mattdeeds/pico-10base-t-rs/docs/router-plan.md

# RP2350 wireless router — design plan

The end goal the whole project serves (see the `project-vision-router` memory):
a **low-power wireless router on the RP2350**. Wireless clients associate on the
LAN side; their traffic is **NAT-routed out the 10BASE-T WAN** to a wired
network / the internet.

With R0–R12e the **WAN half is essentially done** — a robust 10BASE-T NIC
(PIO Manchester TX/RX, edge-track DPLL, multicore RX, carrier-sense + CSMA/CA;
~742 kB/s idle, no starvation, 10–38× better under load than the old
single-core). This doc scopes the **router half**: the wireless LAN, the
forwarding/NAT data path, and how they fit our Hazard3 RISC-V / `rp235x-hal` /
no-embassy stack.

Status: **scoping (2026-05-28).** Architecture fork decided = **Option A**
(keep RISC-V, port the cyw43 transport — see §4). No router code written yet.

---

## 1. Target topology

```
   wireless clients (phones/laptops)
            │  (WPA2, 2.4 GHz)
            ▼
   ┌─────────────────────────────────────────────┐
   │  Pico 2 W (RP2350)                            │
   │                                               │
   │   LAN: CYW43439 in AP mode                    │
   │     • SSID + WPA2, DHCP server, gateway IP    │
   │            │                                  │
   │     ┌──────┴───────┐  forwarding + NAPT       │
   │     │  router core │  (conntrack TCP/UDP/ICMP)│
   │     └──────┬───────┘                          │
   │            │                                  │
   │   WAN: 10BASE-T NIC (R0–R12e)                 │
   │     • DHCP client, default route, DNS         │
   └────────────┼──────────────────────────────────┘
                ▼
        wired LAN / internet
```

The 10BASE-T WAN (~6 Mbit/s effective) is the throughput bottleneck — fine for
a "low-power router." The CYW43 2.4 GHz LAN has headroom to spare.

## 2. What we have vs. what a router needs

| Piece | Have? | Notes |
|---|---|---|
| WAN PHY (10BASE-T) | ✅ R0–R12e | PIO TX/RX, DPLL, multicore RX, CSMA/CA |
| Endpoint stack (the device's own IP) | ✅ smoltcp | ARP/ICMP/UDP/TCP terminate today |
| LAN PHY (wireless AP) | ❌ | CYW43439 in AP mode (§5) |
| DHCP **client** (WAN) | ❌ | smoltcp has a `dhcpv4` socket — small |
| DHCP **server** (LAN) | ❌ | smoltcp has no server — new code (§6.3) |
| L3 **forwarding** between interfaces | ❌ | new — smoltcp won't (§3, §6.1) |
| **NAPT** + connection tracking | ❌ | new — the bulk of the work (§6.2) |
| DNS relay (LAN → WAN) | ❌ | new-ish (§6.4) |
| Management UI | ◑ | reuse the HTTP server on the LAN gateway IP |

## 3. smoltcp's role — keep it, but it is NOT the router

smoltcp is an **endpoint** TCP/IP stack: an `Interface` owns sockets and
terminates traffic addressed to its own IP(s). It has **no packet forwarding
between interfaces and no NAT/NAPT** — it drops anything not addressed to it.

So the router splits cleanly into two planes:

- **Control plane → smoltcp (keep it).** The device's *own* traffic on *both*
  interfaces: DHCP client (WAN), DNS resolver, the management HTTP/UI, ICMP.
  And `cyw43` exposes a **`NetDriver` that plugs straight into a smoltcp
  `Interface`** — the standard, supported LAN glue. Ripping smoltcp out would
  be a mistake; it's doing real work.
- **Data plane → NEW custom code.** Transit packets (a LAN client → the
  internet, and the return path) bypass smoltcp entirely: parse the IP packet,
  NAPT-rewrite it, re-emit on the other interface.

**Architecture = hybrid with a per-frame classifier.** A frame arriving on
either interface is classified:
- **for-us** (dst MAC = our iface MAC, dst IP = our iface IP, broadcast/ARP,
  or a NAPT-return flow) → hand to that interface's smoltcp `Interface`, OR to
  the NAPT reverse path;
- **transit** (routable, not for us) → the forwarding + NAPT fast-path.

This matches the `project-vision-router` instinct ("per-interface raw frames +
our own forwarding/NAPT layer") — but only for the *fast path*; smoltcp stays
the control-plane brain. Two smoltcp `Interface`s (one per phy) coexist with the
forwarding layer; they don't talk to each other through smoltcp.

## 4. The architecture fork — DECIDED: Option A (keep RISC-V)

**The finding that drove this:** the CYW43 driver ecosystem (`cyw43`,
`cyw43-pio`, `embassy-net`) is embassy-centric, and **embassy supports RP2350
only on the ARM Cortex-M33 cores** — to target the **Hazard3 RISC-V** cores you
drop embassy and use `rp235x-hal`, which is precisely our entire codebase. So
the stock wireless stack and our stack sit on opposite sides of an ARM↔RISC-V
line.

Options considered:

| Option | Keeps R0–R12e? | Wireless effort | Decision |
|---|---|---|---|
| **A. Keep RISC-V, port the cyw43 transport** | ✅ all | custom `SpiBusCyw43` + async glue | **CHOSEN** |
| B. Switch the project to ARM + embassy | ❌ rewrite NIC | cyw43 "just works" | rejected — throws away the Hazard3 multicore/PIO/DPLL work |
| C. External wireless (ESP32-AT over SPI) | ✅ | different driver | fallback only — not the onboard radio the user wants |

**Why Option A is feasible** (verified during scoping):
1. `cyw43`'s core driver is **transport-agnostic** via the `SpiBusCyw43` trait;
   `cyw43-pio`'s `PioSpi` is just the embassy-rp reference impl. We write our
   own `SpiBusCyw43` on `rp235x-hal`'s **free PIO1**.
2. `embassy-executor` has a real **`arch-riscv32`** backend (used by ESP32-C3/
   C6, which are riscv32imc/imac) — *separate* from the ARM-only `embassy-rp`
   HAL. So async tasks can run on Hazard3 (`riscv32imac`).
3. A small **`embassy-time-driver`** shim backed by our existing `rp235x-hal`
   `Timer` satisfies cyw43's `Timer::after` delays.

So we pull in `cyw43` (core) + arch-agnostic embassy support crates
(`embassy-executor` arch-riscv32, `embassy-time`, `embassy-sync`,
`embassy-futures`) and skip `embassy-rp` and `cyw43-pio` entirely. The
**biggest new infrastructure + risk is adopting an async runtime** on our
currently-blocking main loop — de-risked first (§7, R13).

## 5. Wireless integration design (Option A)

```
   cyw43 core (transport-agnostic)
     │  SpiBusCyw43 trait
     ▼
   OUR PioSpiCyw43  ── rp235x-hal PIO1 (half-duplex SPI) + DMA + CS/PWR pins
     │
     ├─ Runner::run()  ── async task, driven by embassy-executor (arch-riscv32)
     │                     uses embassy-time (our Timer shim) for delays
     │
     └─ Control         ── async: init(), start_ap_wpa2(SSID, pass), gpio_set(LED)…
     └─ NetDriver       ── impls a Device → smoltcp Interface (LAN control plane)
```

Open items to nail in the R13 spike:
- **Half-duplex SPI PIO program.** The CYW43 uses a nonstandard half-duplex
  SPI (shared data line). Reference: the pico-sdk `cyw43_bus_pio_spi.c` PIO
  program and embassy's `cyw43-pio` — port the program to `rp235x-hal`'s PIO
  API on PIO1.
- **Firmware blobs.** CYW43439 firmware (`43439A0.bin`) + CLM blob, loaded at
  runtime; embed in flash (`include_bytes!`) and feed to `cyw43::new`.
- **Async runtime shape.** embassy-executor on core 0 (restructure `main`'s
  poll loop into async tasks: cyw43 Runner, smoltcp poll×2, router). The
  10BASE-T PIO/DMA/core-1 RX path is IRQ-driven and stays as-is; an async task
  drains its inbox via smoltcp. Decide whether the cyw43 Runner shares core 0
  or moves to core 1 (see §6 core budget).
- **embassy-time-driver** on `rp235x-hal` `Timer` (TIMER0): implement the
  `embassy_time_driver::Driver` trait (now(), schedule_wake()).

## 6. Router data path (the new feature work)

### 6.1 Forwarding
Classify each received frame (§3). Transit IP packets: decrement TTL, look up
the egress interface (LAN-side = the AP subnet; everything else = default route
out WAN), re-emit. Start with plain forwarding (no NAT) tested via static host
routes, then layer NAPT on top.

### 6.2 NAPT + connection tracking
- Outbound (LAN→WAN): rewrite src IP→WAN IP, src port→an allocated port;
  insert/refresh a conntrack entry keyed by (proto, orig-src, orig-sport,
  dst, dport).
- Inbound (WAN→LAN): match the conntrack entry, rewrite dst back to the LAN
  client, re-emit on LAN.
- Per-proto: TCP (track via ports + a coarse state/timeout), UDP (ports +
  idle timeout), ICMP echo (track via id). Fix up IP + L4 checksums on rewrite
  (incremental checksum update).
- Fixed-size conntrack table (heapless) with LRU/timeout eviction — bounded RAM,
  no alloc. This is the bulk of the new code.

### 6.3 DHCP server (LAN)
smoltcp has only a DHCP *client*. The LAN DHCP server is new: a small UDP
responder (DISCOVER→OFFER, REQUEST→ACK) handing out leases from the AP subnet
pool, with gateway = our LAN IP and DNS = our LAN IP (we relay). Fixed lease
table.

### 6.4 DNS relay + management
- DNS: LAN clients use us as resolver; forward their queries out the WAN to the
  upstream DNS (learned via WAN DHCP), relay answers back. (Or run NAPT over the
  DNS UDP flow like any other — simplest is to just NAT port 53 through.)
- Management: reuse the existing HTTP server, bound to the LAN gateway IP —
  status (clients, conntrack, WAN link), and later config.

### Core / PIO / DMA / pin budget
- **PIO:** PIO0 = SM0 10BT-TX, SM1 10BT-RX, SM2 carrier-detect (SM3 free).
  **PIO1 → cyw43 half-duplex SPI** (1 SM). Fits.
- **DMA:** ch0/ch1 = 10BT RX double-buffer; cyw43 SPI wants 1–2 channels —
  available.
- **Cores:** core 0 = main/async-exec/WAN-TX/smoltcp×2/router/USB; core 1 =
  10BT RX decode. The cyw43 Runner + forwarding add load to core 0 — **open
  question:** may need to rebalance (e.g. forwarding fast-path or the cyw43
  Runner on core 1). Measure before deciding.
- **Pins (Pico 2 W):** the CYW43 consumes **GP23 (WL_ON), GP24 (WL_DATA),
  GP25 (WL_CS), GP29 (WL_CLK)**, and the user **LED moves onto the CYW43's own
  GPIO0**. Our 10BASE-T (GP13 RO, GP14 DI) is clear of all of these →
  coexists. **But GP25 (today's `led` pin) becomes WL_CS** — the LED code must
  move to the CYW43 GPIO (via the driver) or another free pin. *(Verify exact
  Pico 2 W pinout in R13.)*
- **Power:** "low-power" fights the always-on 60 MHz RX sampler + continuous
  DMA + cyw43. Deferred to last (roadmap E) — a known unresolved tension.

## 7. Phased roadmap

Riskiest piece (wireless on Hazard3) first, so Option A is proven before we
build the router on top of it.

| Phase | Goal | Acceptance |
|---|---|---|
| **R13 — wireless de-risk spike** | Custom `SpiBusCyw43` on PIO1 + embassy-executor(riscv32) + time-driver shim + CYW43 firmware load. | Chip inits; beacons (AP) or associates (STA); a client sees the SSID / the chip's own LED toggles via the driver. *Proves Option A.* |
| **R14 — LAN up** | CYW43 **AP mode** (WPA2) + smoltcp on its `NetDriver` + **DHCP server**. | A phone joins the SSID, gets a DHCP lease, pings the Pico's LAN gateway IP. |
| **R15 — WAN as client** | **DHCP client** on the 10BASE-T (smoltcp `dhcpv4`) → upstream IP, default route, DNS. | The Pico itself reaches the internet (ping 8.8.8.8, resolve a name). |
| **R16 — forwarding** | L3 forward LAN↔WAN for transit packets (static routes, no NAT). | A LAN client with a manual route reaches a WAN host. |
| **R17 — NAPT** | NAT/NAPT + conntrack (TCP/UDP/ICMP) + the per-frame classifier. | **A phone on WiFi browses the internet through the Pico.** The milestone. |
| **R18 — DNS relay + mgmt UI** | LAN DNS relay; HTTP status/config on the LAN gateway IP. | Clients resolve names via the Pico; mgmt page shows clients + WAN link. |
| **R19+ — robustness, backpressure, then low-power** | Flow control, conntrack pressure handling; then the deferred power work. | — |

## 8. Risks + open questions

1. **Async runtime adoption (R13, the #1 risk).** embassy-executor on
   `riscv32imac` is real but unproven *in this project*; restructuring the
   blocking main loop into async tasks touches everything. De-risk in R13 with
   the minimum (just blink the CYW43 LED via async) before committing.
2. **Half-duplex SPI PIO port.** The CYW43 SPI program must be ported to
   `rp235x-hal` PIO1. The pico-sdk C program + cyw43-pio are the references.
3. **Core balance.** cyw43 Runner + NAPT forwarding + two smoltcp polls on
   core 0 may not fit; rebalancing onto core 1 (which currently only decodes
   10BT RX) is the likely lever — measure, don't assume (the project's MO).
4. **Memory.** Two smoltcp `Interface`s + socket buffers + conntrack + DHCP/
   ARP tables + cyw43 firmware + core-1 stack. RP2350 has 520 KB SRAM — should
   fit, but budget it.
5. **Low-power vs always-on sampler** — unresolved; explicitly last.
6. **cyw43 on Hazard3 has little/no precedent** — we may hit
   embassy-executor/embassy-time integration rough edges that the ARM path
   doesn't. Keep Option C (external module) as the fallback if R13 stalls.

## 9. References

- cyw43 driver + AP mode + RP2350/Pico 2 W support: <https://docs.embassy.dev/cyw43>,
  <https://github.com/embassy-rs/embassy/tree/main/cyw43>
- embassy RISC-V on RP2350 = drop embassy, use rp235x-hal (ARM-only embassy):
  <https://riscv.org/blog/raspberry-pi-launch-new-rp2350-microcontroller-and-pico-2-development-board-with-risc-v-support/>
- embassy-executor `arch-riscv32`:
  <https://github.com/embassy-rs/embassy/blob/main/embassy-executor/src/arch/riscv32.rs>
- `SpiBusCyw43` / custom transport + the half-duplex SPI PIO:
  <https://github.com/embassy-rs/embassy/blob/main/cyw43-pio/src/lib.rs>,
  <https://github.com/raspberrypi/pico-sdk/blob/master/src/rp2_common/pico_cyw43_driver/cyw43_bus_pio_spi.c>

## 10. R13 progress — board-independent scaffolding DONE (2026-05-28)

Built on branch `r13-wireless-scaffold` (not merged). Gated behind a new
`wireless` cargo feature, OFF by default — the production 10BASE-T build is
byte-unchanged. **`cargo build --release --features wireless` compiles AND
links for `riscv32imac`.**

**De-risking results (the reason for the spike):**
- **cyw43 0.7.0 + its ARM-named deps (`cortex-m` 0.7.7, `cortex-m-rt` 0.7.5)
  compile for riscv32imac.** The fear that `cortex-m-rt` would `compile_error!`
  on non-ARM was wrong — it target-gates to ~nothing. So Option A is viable.
- **`embassy-executor` 0.10 `platform-riscv32` backend links on Hazard3** —
  the #1 risk (async runtime on RISC-V, separate from the ARM-only
  `embassy-rp`) is cleared at the link level.
- Compatible version set pinned by cyw43 0.7.0: embassy-time 0.5.1 (with
  `tick-hz-1_000_000` + `generic-queue-16`), embassy-time-driver 0.2.2,
  embassy-time-queue-utils 0.3.2, embassy-sync 0.8.0, embassy-futures 0.1.2.
  The executor feature is `platform-riscv32` (renamed from `arch-riscv32`).
- embassy-executor 0.10's `#[task]` macro returns a `Result<SpawnToken,_>`
  (arena slot) — spawn via `if let Ok(t) = task() { spawner.spawn(t) }`.

**What's in `src/wireless.rs` (compiles + links, not yet run on hardware):**
1. **embassy-time driver on TIMER0** — `now()` reads the µs counter (1 MHz tick
   = no scaling); `schedule_wake()` uses ALARM0 + the `TIMER0_IRQ_0` handler +
   the generic 16-slot timer queue. The RP2350 TIMER0 PAC accessors
   (`timerawh/l`, `alarm0`, `inte.alarm_0`, `intr` write-1-to-clear) all
   resolved correctly.
2. **Async executor** — `run_executor()` enables the alarm IRQ, then runs the
   `embassy-executor` thread executor with a heartbeat task that `await`s an
   `embassy_time::Timer` (which link-exercises the whole time stack).
3. **`SpiBusCyw43` transport skeleton** — `PioSpiCyw43` + the trait impl
   (`cmd_write`/`cmd_read`) type-check against `cyw43::new`'s bounds. **Bodies
   are stubs** — the real half-duplex gSPI PIO1 program is the on-board step.

**Remaining for R13 (needs the Pico 2 W in hand):**
- Port the gSPI PIO program to PIO1 + fill in `cmd_write`/`cmd_read` (FIFO/DMA).
  Refs: pico-sdk `cyw43_bus_pio_spi.c`, embassy `cyw43-pio`.
- Embed the CYW43 firmware + CLM blobs (`cyw43-firmware`).
- Build `PioSpiCyw43` + the PWR (WL_ON) pin, call `cyw43::new(...)`, spawn
  `Runner::run()`, `Control::init()` → toggle the onboard LED / beacon.
- Verify on-wire: chip inits; a client sees the SSID. (R14 then adds AP +
  DHCP server + the smoltcp LAN `Interface`.)
- Relocate the user LED off GP25 (= wireless CS on Pico 2 W).

## 11. R13 on-board findings + the pivot (2026-05-28)

Pico 2 W in hand. **Production 10BASE-T verified clean on the new board**
(ping 100%, curl 200, UDP 10/10, core 1 + carrier-sense all working) — the WAN
side fully survived the swap (GP13/14 unchanged).

**Synchronous gSPI bit-bang probe result: chip not responding.** The probe
(`wireless::probe_cyw43`) powers WL_ON and bit-bangs `read32_swapped(TEST_RO)`,
expecting `0xFEEDBEAD`. It reads **varying** values (first `0x06060606`, last
`0xfdda7d5b`, `stable=0`) → DATA is floating/undriven → the CYW43 isn't
responding (power, or the command isn't reaching it), not a mere framing offset.
- **Ruled out:** pin map (GP23=WL_ON, 24=DATA, 25=CS, 29=CLK — confirmed for
  Pico 2 W) and SIO funcsel (`= 5` on RP2350, same as RP2040).
- **Wall:** the CYW43 SPI lines are NOT exposed on the header, so they can't be
  scoped — blind bit-bang timing/power iteration is inefficient and low-yield
  (the bit-bang also can't replicate the PIO input-synchronizer timing the chip
  expects).

**Decision: pivot to the proven `cyw43` driver + a faithful PIO gSPI transport
(known-good timing).** With the board verified good (UPDATE below), the open
question is purely our transport — so **Step 1 proves it directly** (a sync
TEST_RO read), and cyw43's `init()` `while != FEEDBEAD` handshake is then a later
end-to-end confirmation, not the first-line test. An `init` hang ⇒ debug the
PIO/transport, not the board.

**UPDATE (2026-05-28) — board verified GOOD; plan refined.** Stock MicroPython
v1.28.0 (`RPI_PICO2_W`, driven over the REPL with `mpremote`) proved the board:
`Pin('LED')` toggles (CYW43 + gSPI bus alive) and `WLAN.scan()` returned 12 APs
(CYW43 MAC `2c:cf:67:df:78:2f`, RPi OUI). **⇒ The hardware is fine — our gSPI
code is the bug**, so an `init` hang now points at our transport, not the board.

**Definition of done (R13):** `[Cyw43] init done` over CDC + onboard LED blink
via `Control::gpio_set(0,..)`. Proves (a) the PIO1 gSPI transport drives the chip
with timing it accepts and (b) the embassy async runtime carries cyw43 on Hazard3
at *runtime*. Bonus: a scan echoing the MicroPython 12-AP baseline.

**Structural decision — R13 is a *standalone* wireless build.** The embassy
executor's `run()` seizes core 0 and never returns, so it can't coexist with the
blocking 10BASE-T main loop. `--features wireless` builds a wireless-only image
(clocks + USB + PIO1 gSPI → executor tasks); 10BASE-T isn't started. Running both
interfaces concurrently (the real router) is **R14+** and needs a runtime
unification (10BT phy in an async task, or its RX IRQ on core 1 while the executor
owns core 0) — out of R13 scope.

**Build steps (cheapest de-risk first):**
1. **PIO1 gSPI transport, proven *synchronously* against TEST_RO first.** Write
   the self-contained FIFO-driven gSPI program on PIO1 (`pull` write-count→X,
   read-count→Y, then words; side-set CLK=GP29; **MSB-first** ⇒ OUT/IN shiftdir =
   `Left`; **DATA=GP24 must be in the OUT, SET *and* IN pin groups** — `out pins,1`
   drives it, `set pindirs,0` turns it around, `in pins,1` samples it; autopush;
   CS=GP25 as SIO around the txn). **Before any async/firmware**, expose a
   *blocking* `pio_cmd_read(TEST_RO)` from the existing probe slot (`main.rs:172`),
   reusing today's CDC/UDP telemetry. **For this probe, clock `cmd(32)` out + read
   one 32-bit word in** and read `0xFEEDBEAD` from it — no trailing status word is
   needed here (cyw43 enables `STATUS_ENABLE` only *after* the bus test, and we're
   not going through cyw43's `Bus` yet; matches the proven bit-bang). A trailing
   status word is harmless if you reuse the Step-2 `cmd_read` path with `len=1`.
   This isolates the one unproven thing — our PIO timing vs the chip — from the
   whole async+firmware stack; `0xFEEDBEAD` ⇒ transport proven. Template: the
   rp235x-hal idiom in `eth_tx.rs::new`; port the program from embassy `cyw43-pio`
   + pico-sdk `cyw43_bus_pio_spi.c`; reuse `probe_cyw43`'s `cmd_word`/`swap16`. If
   it fails, bring the attached **CMSIS-DAP debug probe (ttyACM0) + OpenOCD** in
   for register/step visibility on the off-header lines.
2. **Async `SpiBusCyw43` impl.** Move the proven FIFO push/pull into
   `PioSpiCyw43::cmd_write/cmd_read` (replace the `wireless.rs` stubs). Busy-poll
   the FIFO inside the async fn for R13 (DMA later). Bit counts: `cmd_write` clocks
   `write.len()*32` bits out; `cmd_read` clocks `32` cmd bits out, then
   `(read.len()+1)*32` bits in — `read.len()` data words **plus one trailing
   status word**, which is the `u32` cmd_read returns (the backplane's extra
   *leading* word is already counted in `read.len()`, sized by cyw43's caller — so
   don't add it twice). **Confirmed:** the 16-bit init swap lives in cyw43's `Bus`
   (`read32_swapped` does `swap16` in/out), so our transport just clocks raw
   MSB-first words — no swap of our own.
3. **Firmware blobs + `cyw43::new`.** ⚠️ 0.7.0 needs **three** blobs:
   `new(state, pwr, spi, firmware, nvram)` (both `cyw43::Aligned<A4,_>` —
   re-exported, no new dep) **plus** CLM via `Control::init(clm)`. The original
   "fw+CLM" was incomplete — the **nvram** blob is required, and sourcing the right
   one for the 0.7.0 API is a top unknown (verify vs 0.7.0 docs / the matching
   embassy tag). Then: `State::new()` (a `const fn`) into a `&'static mut` via the
   `MaybeUninit`-static pattern `run_executor` already uses; build `PioSpiCyw43` +
   WL_ON (GP23) + GP25 CS; `cyw43::new(..).await` → spawn `Runner::run()` →
   `Control::init(clm)` → `gpio_set(0,true)`. **GP25 is now the gSPI CS, not the
   `main.rs:163` LED.** Watch TIMER0 ownership (the time driver owns ALARM0 +
   `TIMER0_IRQ_0` — don't also give TIMER0 to `hal::Timer`).
4. **Telemetry-in-async.** Log ring buffer + an executor task polling usbd-serial
   (+ the `pico_reset` interface, to keep `cargo run` reflashing) so init
   progress/panics are visible over CDC. **Spawn this telemetry task (and the
   heartbeat) *before* the cyw43 bring-up, and log a milestone before each init
   stage** — `cyw43::new()` does `runner.init(...).await.unwrap()`, so most
   failures panic (caught by our panic handler), but the bus handshake can *spin*;
   per-stage logs + a live heartbeat make a hang localizable. Note: cyw43's
   `firmware-logs` is **inert without a `log`/`defmt` backend** (its macros no-op
   otherwise), so don't rely on it — emit our own `[Cyw43] …` milestones.
5. **Observe:** `[Cyw43] init done` + LED blink ⇒ R13 met. Then R14: AP + DHCP
   server + the smoltcp LAN `Interface`.

**Risks:** PIO gSPI timing (the core unknown — Step 1 isolates it) · nvram blob
sourcing for 0.7.0 · async links-but-misbehaves at runtime (heartbeat + Step-1
telemetry surface it) · TIMER0/IRQ/CS conflicts (standalone build avoids 10BT
contention) · executor ⊥ 10BT concurrency (deferred to R14).

## 12. R14 — "LAN up": concrete step plan (2026-05-29)

R13 proved the chip inits over our PIO1 transport (`[Cyw43] new=1 init=1 led=1`)
via `block_on`. R14 turns that one-shot bring-up into a **live LAN**: an AP a
phone can join, a DHCP server that leases it an address, and a smoltcp
`Interface` on the wireless side that answers from the gateway IP.

**Goal / acceptance (= §7's R14 row, unchanged):** *a phone joins the SSID, gets
a DHCP lease, and pings the Pico's LAN gateway IP.* That is the whole bar.

**Scope is deliberately NARROW — LAN-side only.** R14 does **not** include
WAN-as-client (R15), L3 forwarding (R16), or NAPT/conntrack (R17). (The RESUME's
older "AP + DHCP + NAPT" phrasing conflated those; this §12 + the §7 table are
authoritative — NAPT stays R17.) Because the acceptance is purely LAN-side, R14
**stays a standalone-wireless build** (`--features wireless`, 10BASE-T not
started, per §11). The hard executor-⊥-10BT runtime unification is **R16's**
problem, when transit traffic must actually cross the two interfaces.

### 12.1 Two architecture decisions (DECIDED)

**(1) Runtime model = the persistent embassy executor (DECIDED, not `block_on`).**
R13's `block_on(select(runner.run(), seq))` *returned* after the 6-blink
sequence — the Runner died. R14 needs `Runner::run()` alive **forever** (it
services every gSPI transaction + chip event). We graduate to the real
executor: `run_executor()` (already compiles + links since R13, but never yet
*run* on hardware) spawns the Runner + a net task + the USB/telemetry task.
Running the executor for the first time in this LAN-only setting **retires the
project's documented #1 risk** (async runtime on Hazard3 at runtime, §8.1) at low
stakes — no 10BT to corrupt if it misbehaves. **Fallback if the executor hangs
at runtime:** `block_on(join3(runner.run(), net_loop(), usb_loop()))` reuses
R13's exact proven primitive; the LAN logic below is identical either way.

**(2) The `NetDriver` → smoltcp glue is a `phy::Device` ADAPTER we write — NOT a
direct plug (corrects §3).** §3 claimed cyw43's `NetDriver` "plugs straight into
a smoltcp `Interface`." Verified false for *raw* smoltcp (what `EthMac` uses on
the 10BT side): `cyw43::NetDriver<'a> = embassy_net_driver_channel::Device<'a,
MTU>`, which implements the **async, waker-based `embassy_net_driver::Driver`**
trait — that plugs into *embassy-net*, not raw smoltcp's synchronous
`phy::Device`. **CORRECTION (R14.3, after building it):** an earlier draft of
this section claimed `ch::Device` also exposes a synchronous
`try_rx_buf`/`try_tx_buf`/`borrow_split` API we could shim over directly. **That
was wrong** — those methods live on the *producer-side* `ch::Runner` (and
`Rx/TxRunner`), which **cyw43's `Runner` owns internally and never exposes**; the
`NetDriver` we get is consumer-only and async-Driver-only. The actual bridge
(`src/cyw43_phy.rs`): call the async `Driver::receive`/`transmit` with a
**no-op-waker `Context`** — they're poll-style (`Some(tokens)` when ready, else
`None` after registering the waker we discard), which *is* smoltcp's synchronous
`phy::Device` contract since our net task re-polls on its own cadence. Still **no
`embassy-net` dependency** (just the `embassy-net-driver` trait crate, pinned to
cyw43's version), one smoltcp stack for both interfaces. This adapter is the
keystone new piece — **proven on-device: a Wi-Fi client pings `192.168.4.1`
5/5.**

### 12.2 Steps (lowest-risk increment first; each has its own on-wire accept)

| Step | Work | Acceptance |
|---|---|---|
| **R14.1 — continuous Runner** | Replace `cyw43_bringup_blocking`'s `select→return` with: `cyw43::new()` → `Control::init(clm)` → **spawn `Runner::run()` as a long-lived executor task**, keep `Control` live. Relocate the heartbeat LED to `Control::gpio_set(0,…)` (GP25 is now WL_CS — retire `main.rs:163`'s `led`). | LED blinks **indefinitely** (not just 6×) ⇒ Runner stays up under the executor. The core de-risk — everything else builds on it. |
| **R14.2 — start AP** | After init: `Control::start_ap_wpa2(SSID, passphrase, channel)` (sig confirmed, cyw43 0.7.0). Read the MAC via `Control::address()`. | The SSID appears in a phone/laptop wifi scan. |
| **R14.3 — phy adapter + LAN `Interface`** ✅ DONE (`5039a11`) | New `src/cyw43_phy.rs`: `Cyw43Phy` wraps the `NetDriver` and bridges its async `embassy_net_driver::Driver` to smoltcp `phy::Device` via a **no-op-waker `Context`** (NOT the sync buf API — see §12.1 correction). `receive`/`transmit` map the embassy tokens to smoltcp tokens (delegating `consume`). Stop dropping `_net`; build a 2nd smoltcp `Interface` (static `192.168.4.1/24`, MAC from `Control::address()`) in a `net_task` poll loop (no sockets — ARP + auto-icmp-echo-reply answer from the Interface). | ✅ A client (host RTL88x2bu) joined the AP, static `192.168.4.2/24`, **`ping 192.168.4.1` = 5/5 ~6 ms**; device `rx` counter climbed in step. Data path proven both directions before DHCP. |
| **R14.4 — DHCP server** (§6.3; the bulk) ✅ DONE (`364281f`) | New `src/dhcp_server.rs`: smoltcp UDP socket on `:67`; reuses smoltcp's `DhcpRepr`/`DhcpPacket` wire codec (wireless-only `proto-dhcpv4` feature) — DISCOVER→OFFER, REQUEST→ACK; yiaddr from a fixed MAC-keyed pool `192.168.4.10..=.41`, router + server-id = `192.168.4.1`, /24 mask, 1 h lease; broadcast to `255.255.255.255:68`. **No DNS option** (R18; also avoids smoltcp's heapless-0.9 `dns_servers` Vec vs our 0.8). | ✅ host RTL88x2bu client: **`DHCPACK of 192.168.4.10 from 192.168.4.1`**; device `dhcp` counter climbed. The "LAN up" milestone — join + auto-lease (ping proven R14.3). |
| **R14.5 — mgmt sanity + docs** ✅ DONE (`a745875`) | `net_task` gains a TCP `:80` socket + `serve_status_http` (one-shot HTTP/1.0) showing AP SSID, LAN gateway, uptime, DHCP/rx counters. | ✅ joined client `curl http://192.168.4.1/` returned the status page (uptime 124 s, LAN rx 5). **R14 "LAN up" COMPLETE.** |

### 12.3 Risks (R14-specific)

1. **First on-hardware executor run** (R14.1) — the #1 deferred risk finally
   exercised. Mitigated by the `block_on(join)` fallback (12.1).
2. **DHCP broadcast quirks** — clients send from `0.0.0.0` → `255.255.255.255`
   *before* they hold an IP; the smoltcp UDP socket bind / broadcast-accept + the
   BOOTP broadcast flag are the fiddliest new code. Budget time here.
3. ~~**Adapter borrow model**~~ — RESOLVED (R14.3): the async `Driver::receive`
   already returns the rx+tx token pair co-borrowing the `NetDriver`, so the
   smoltcp `phy::Device` lifetimes line up with no `borrow_split` needed. The
   real surprise was the *mechanism* (noop-waker over the async Driver, not a
   sync buf API) — see the §12.1 correction.
4. **gSPI at 2 MHz busy-poll** — the *continuous* Runner now does ongoing SPI
   (not one-shot init); fine for LAN-only R14, but DMA on the transport (deferred
   in §11) becomes wanted at R16 when the core is also forwarding.
5. **Memory** — 2nd `Interface` + socket buffers + cyw43 `State`. The 231 KB
   firmware is in *flash* (`include_bytes!`), not RAM. Budget against 520 KB.
6. **Validation gotcha (R14.4): the DHCP gateway hijacks the test host's default
   route.** Our server correctly hands out `router = 192.168.4.1`; a normal DHCP
   client (`dhclient`/NetworkManager) installs that as the host's *default
   route*, so all internet/SSH traffic gets sent to the Pico — which can't
   forward yet (NAT is R17) — and the box loses connectivity. When validating
   from a multi-homed host (Wi-Fi + a real uplink), run the DHCP client so it
   does NOT touch routing: `dhclient -v -1 -sf /bin/true <wlan>` proves the
   exchange (prints `bound to 192.168.4.x`) and configures nothing; then
   `ip addr add <leased-ip>/24 dev <wlan>` for the ping. (Goes away naturally
   once the Pico actually NAT-forwards at R17, or test from a phone with no
   other uplink.)
